Sadrita404/Nano-Spark/BILL/bill 1.png

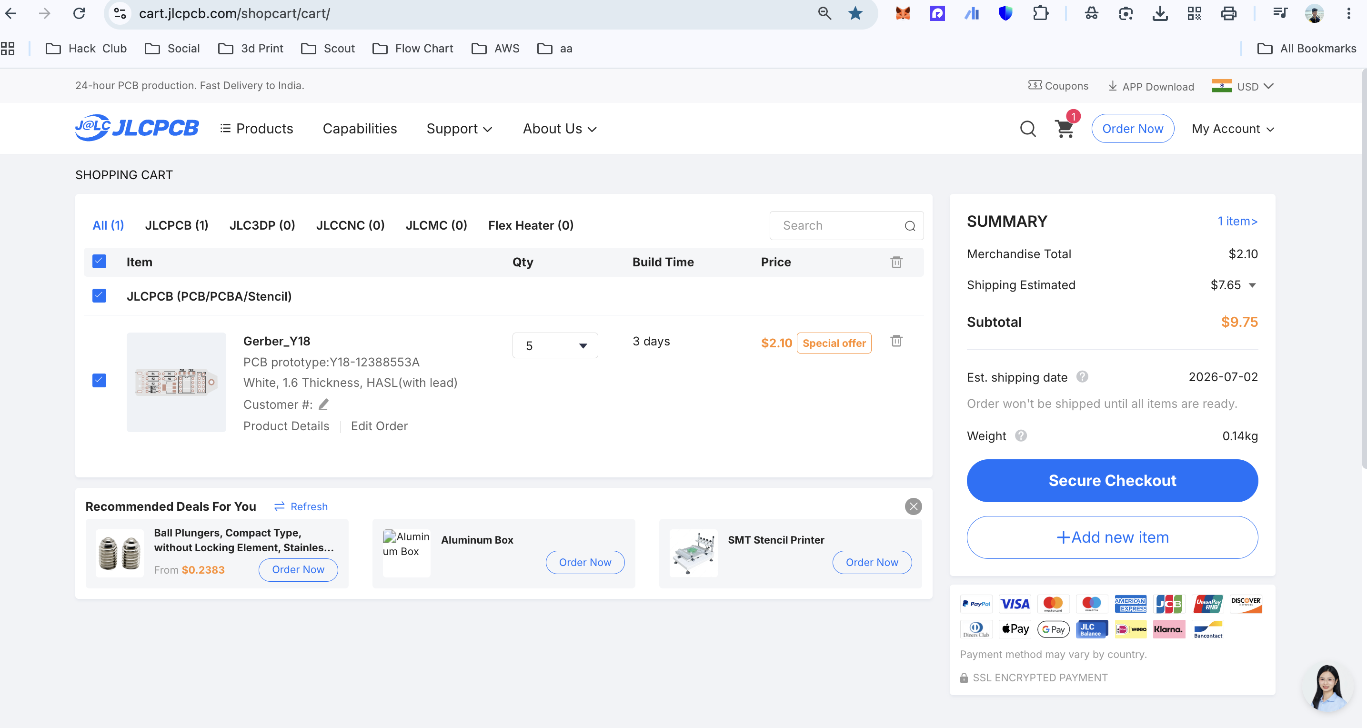
BILL/bill 1.png
