Sadrita404/Nano-Spark/BILL/bill 2.png

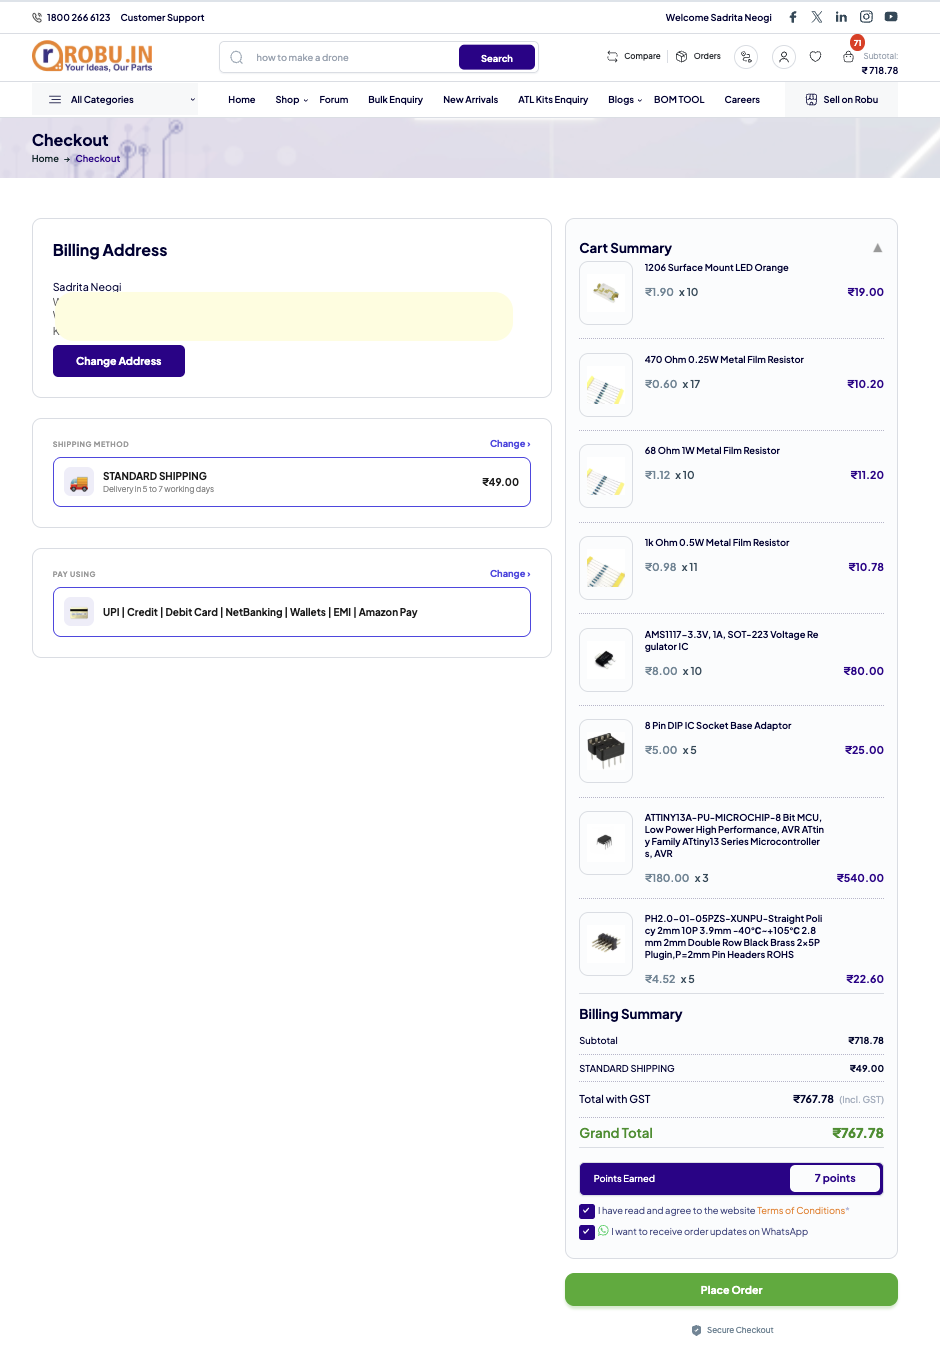
BILL/bill 2.png
