Sadrita404/Nano-Spark/BILL/bill 3.png

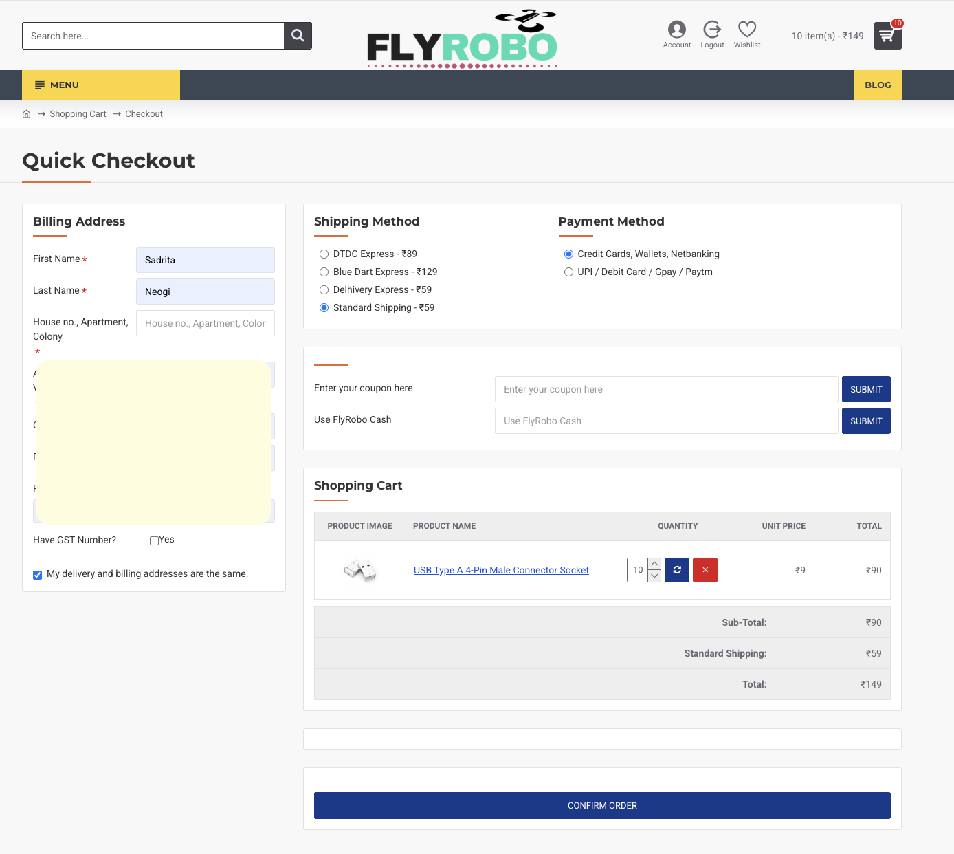
BILL/bill 3.png
