Sadrita404/Nano-Spark/Images/1.png

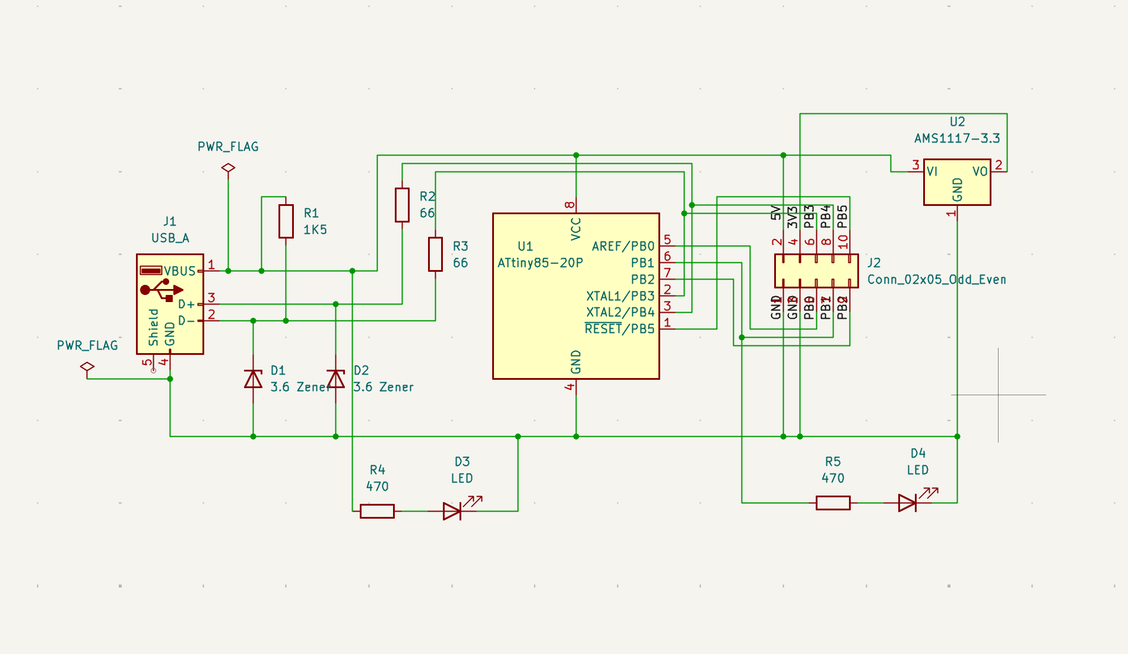
Images/1.png
