Sadrita404/Nano-Spark/Images/2.png

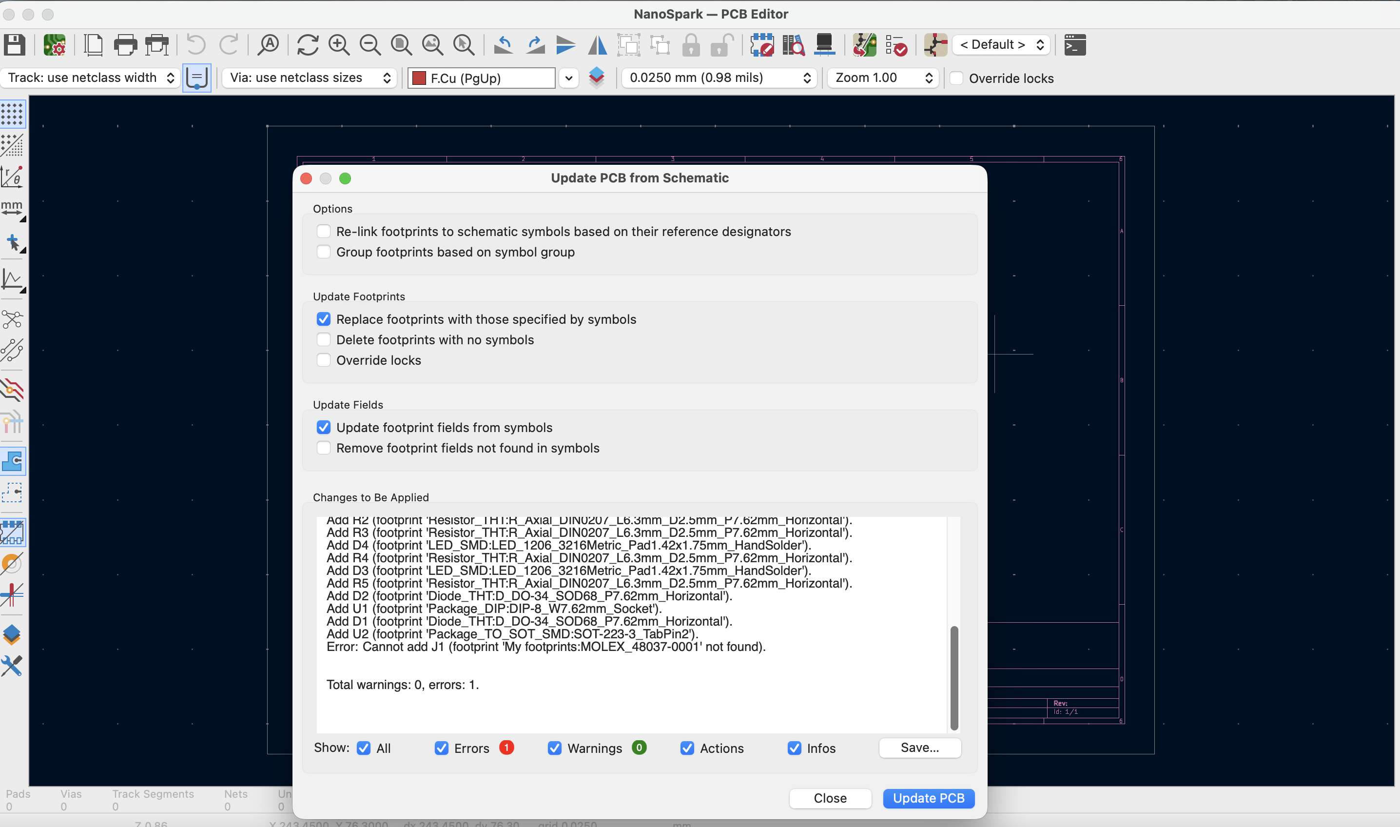
Images/2.png
