Sadrita404/Nano-Spark/Images/3.png

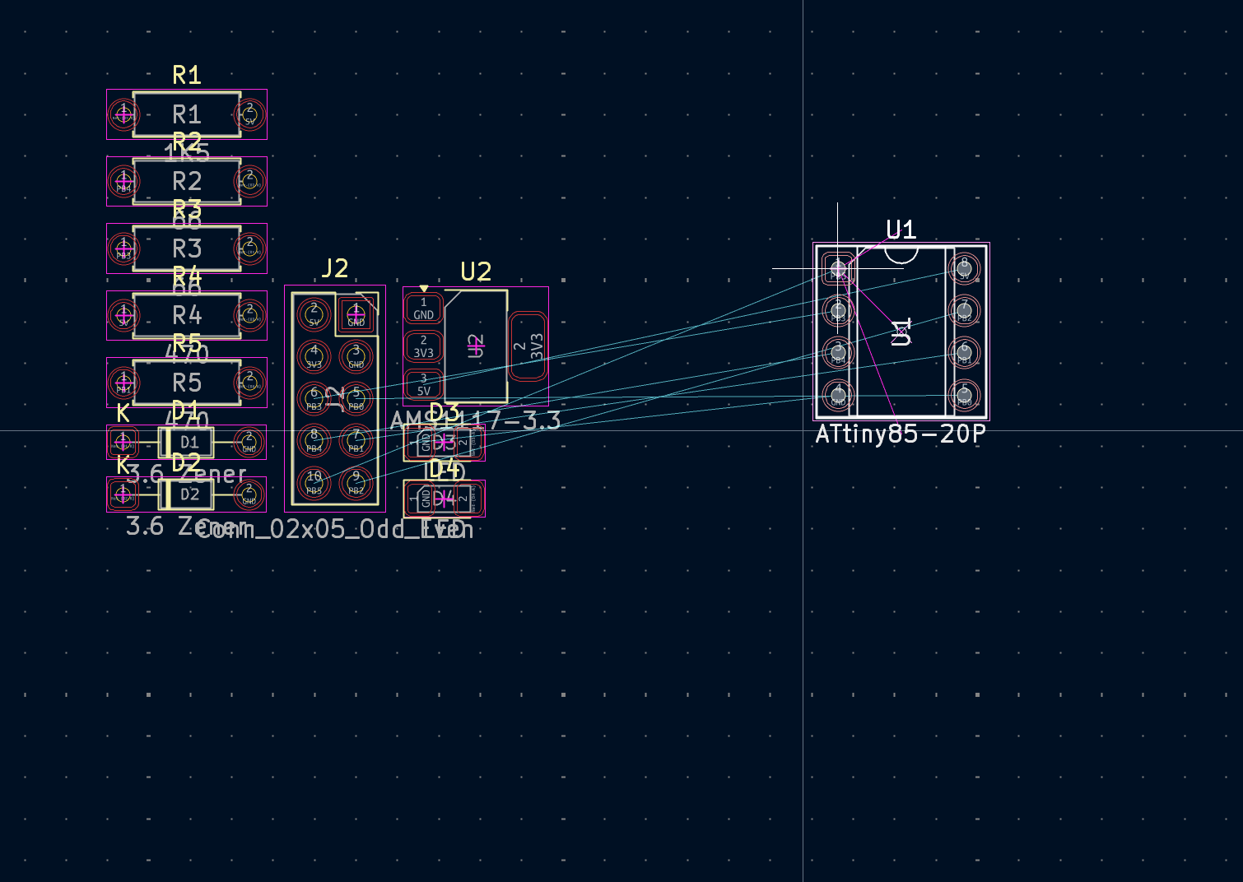
Images/3.png
