Sadrita404/Nano-Spark/Images/4.png

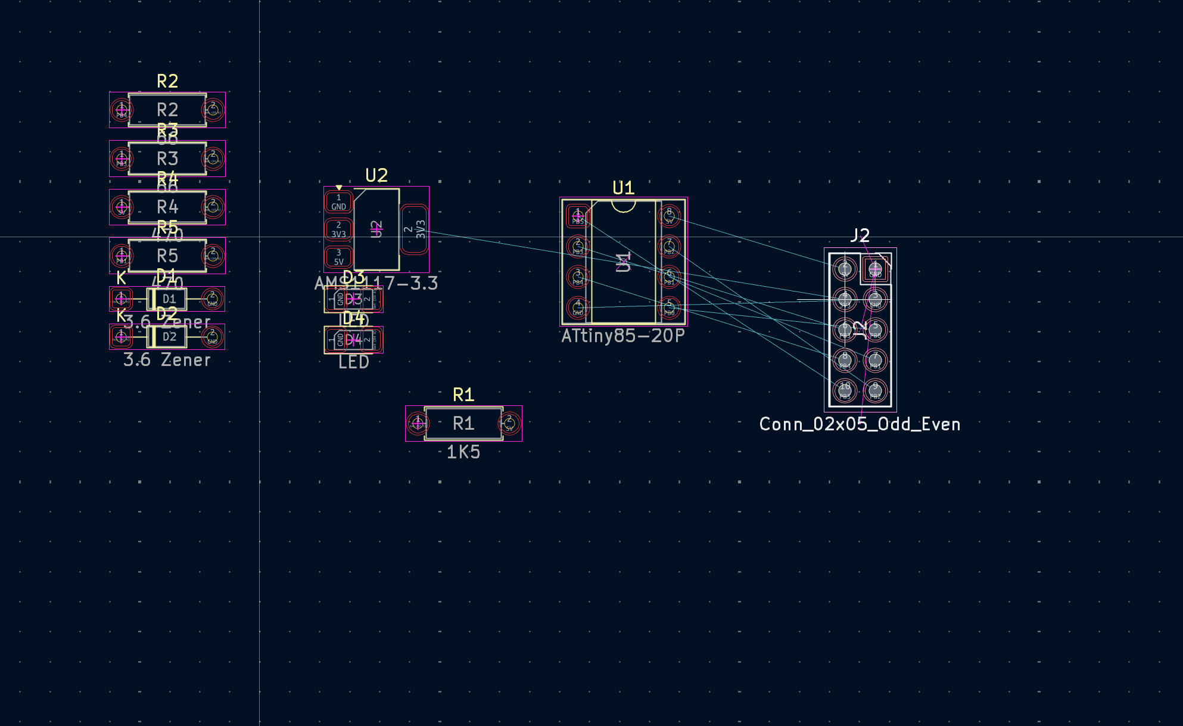
Images/4.png
