Sadrita404/Nano-Spark/Images/5.png

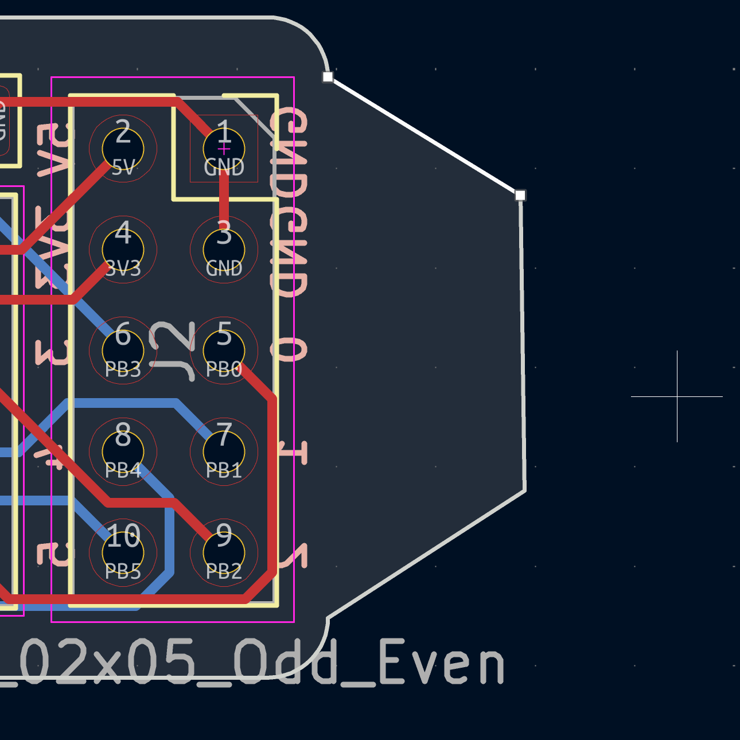
Images/5.png
