Sadrita404/Nano-Spark/Images/6.png

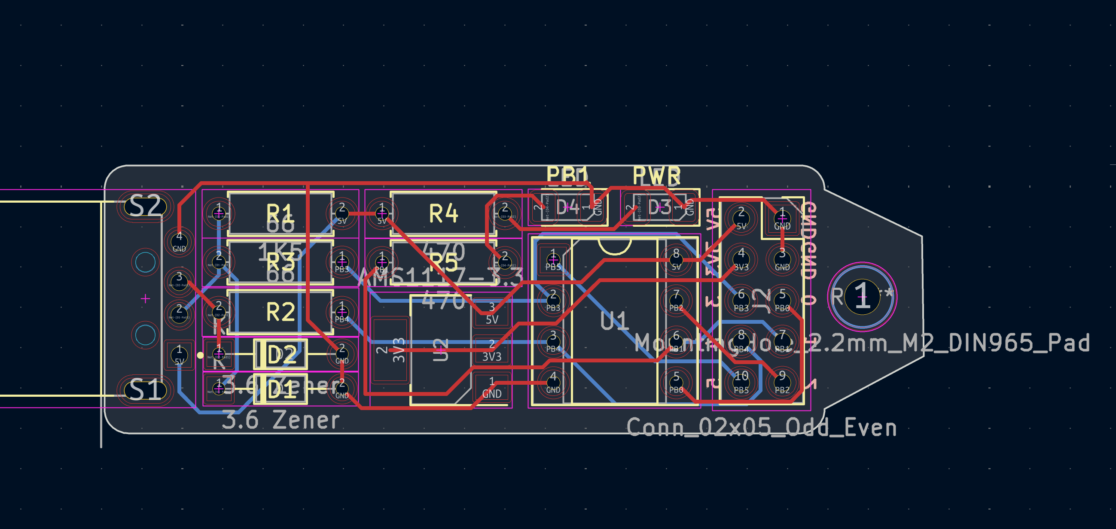
Images/6.png
