Sadrita404/Nano-Spark/Images/7.png

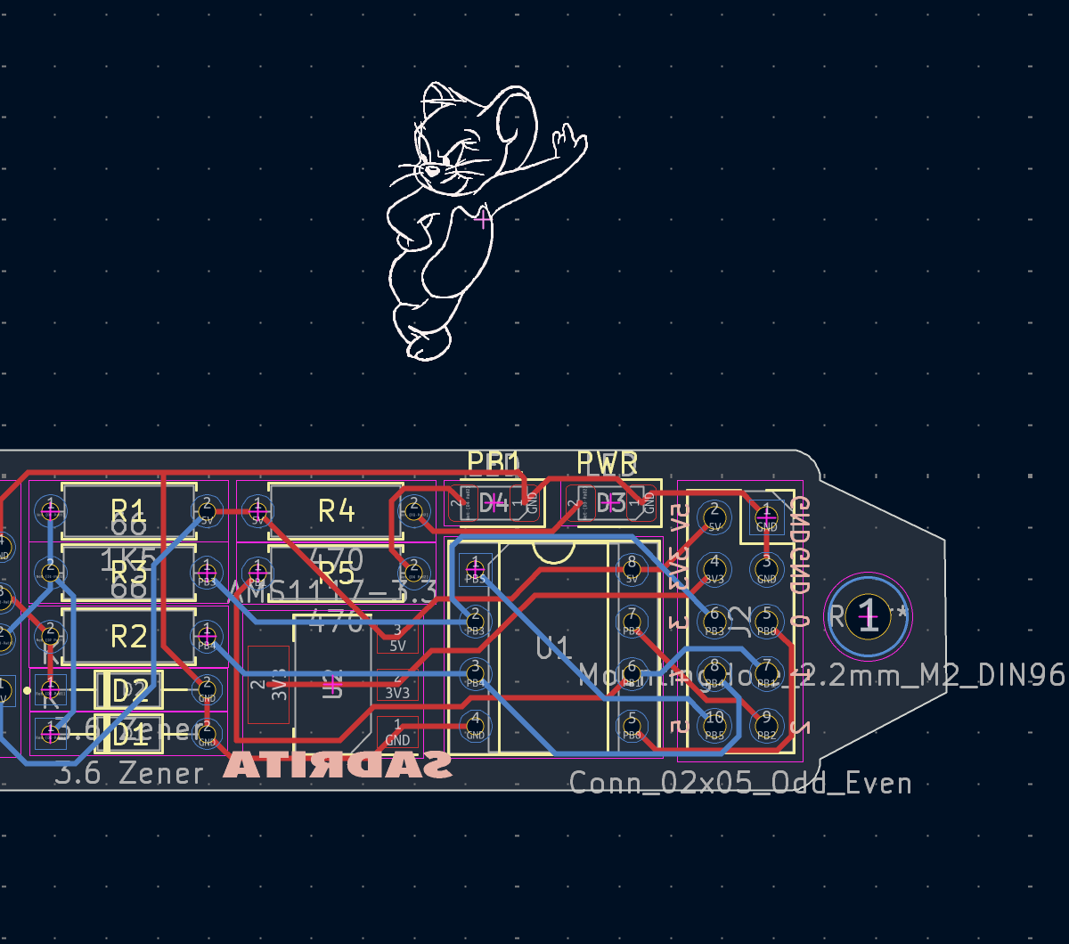
Images/7.png
