Sadrita404/Nano-Spark/Images/8.png

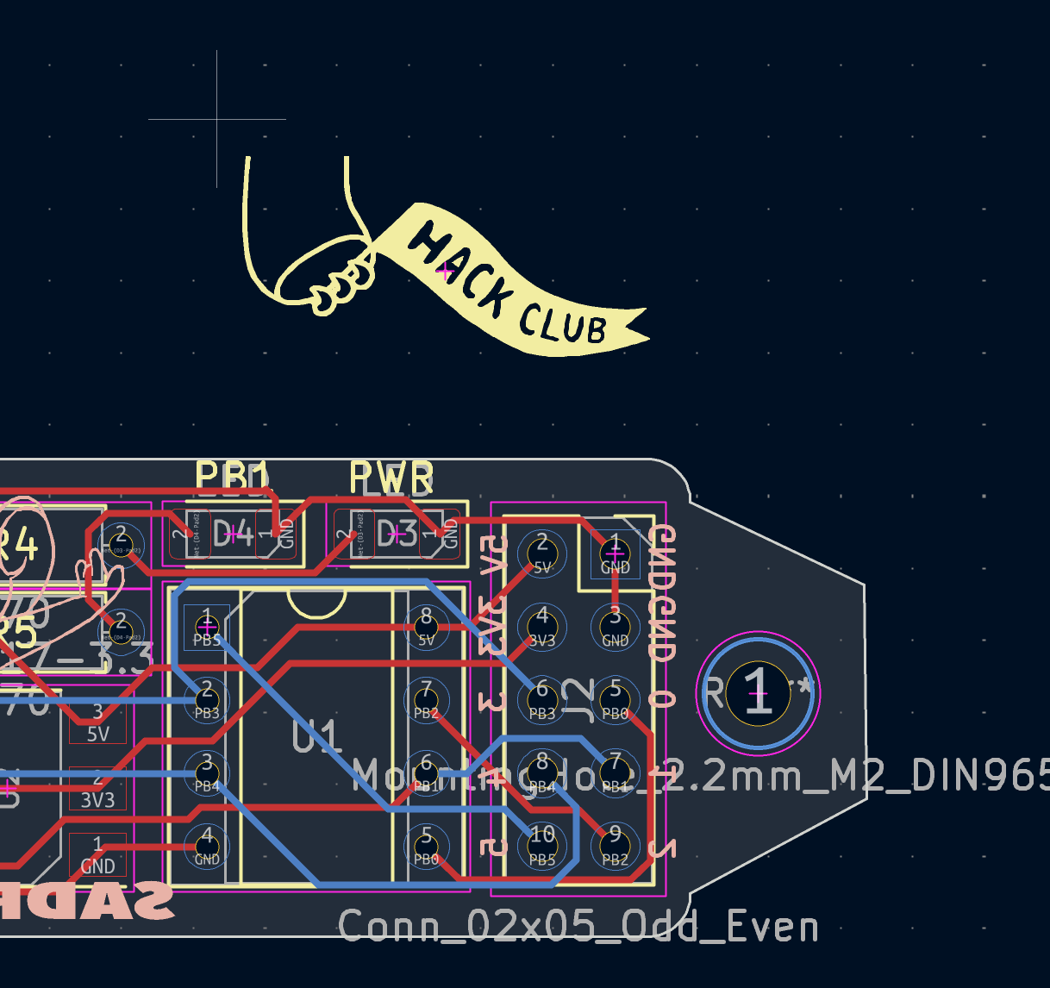
Images/8.png
