Sadrita404/Nano-Spark/Images/9.png

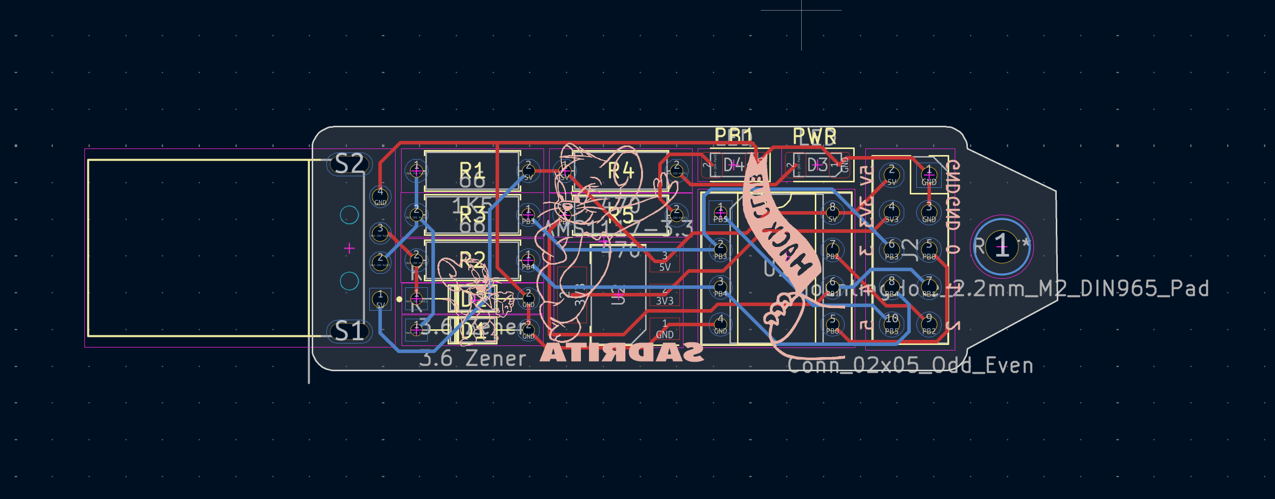
Images/9.png
