Sadrita404/Nano-Spark/Images/10.png

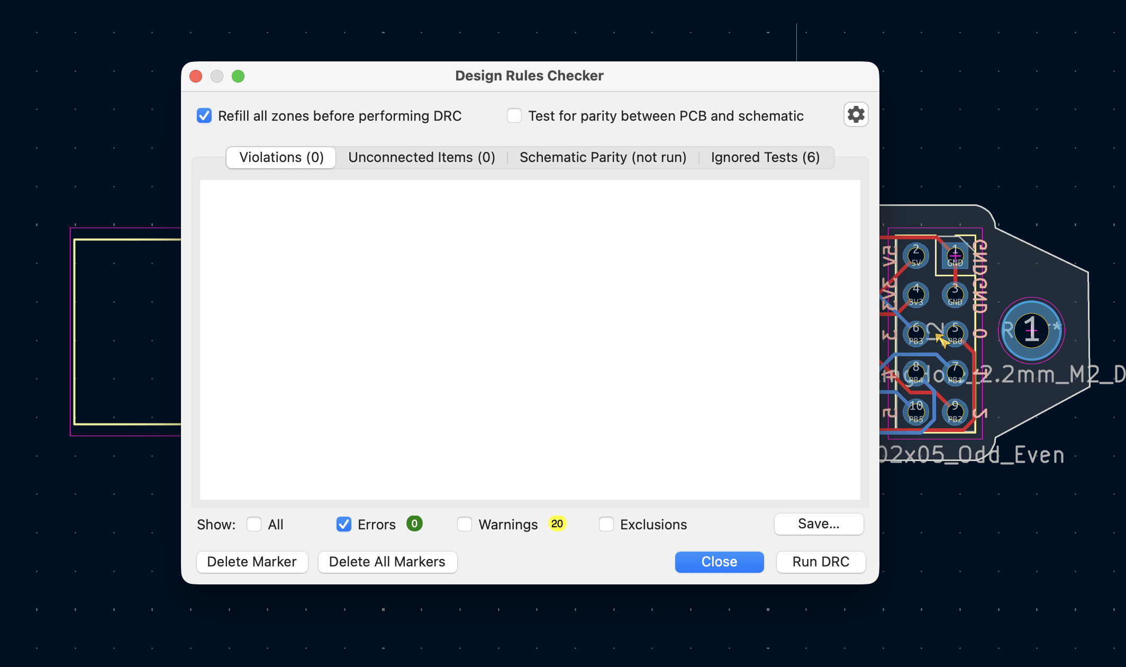
Images/10.png
