Sadrita404/Nano-Spark/Images/11.png

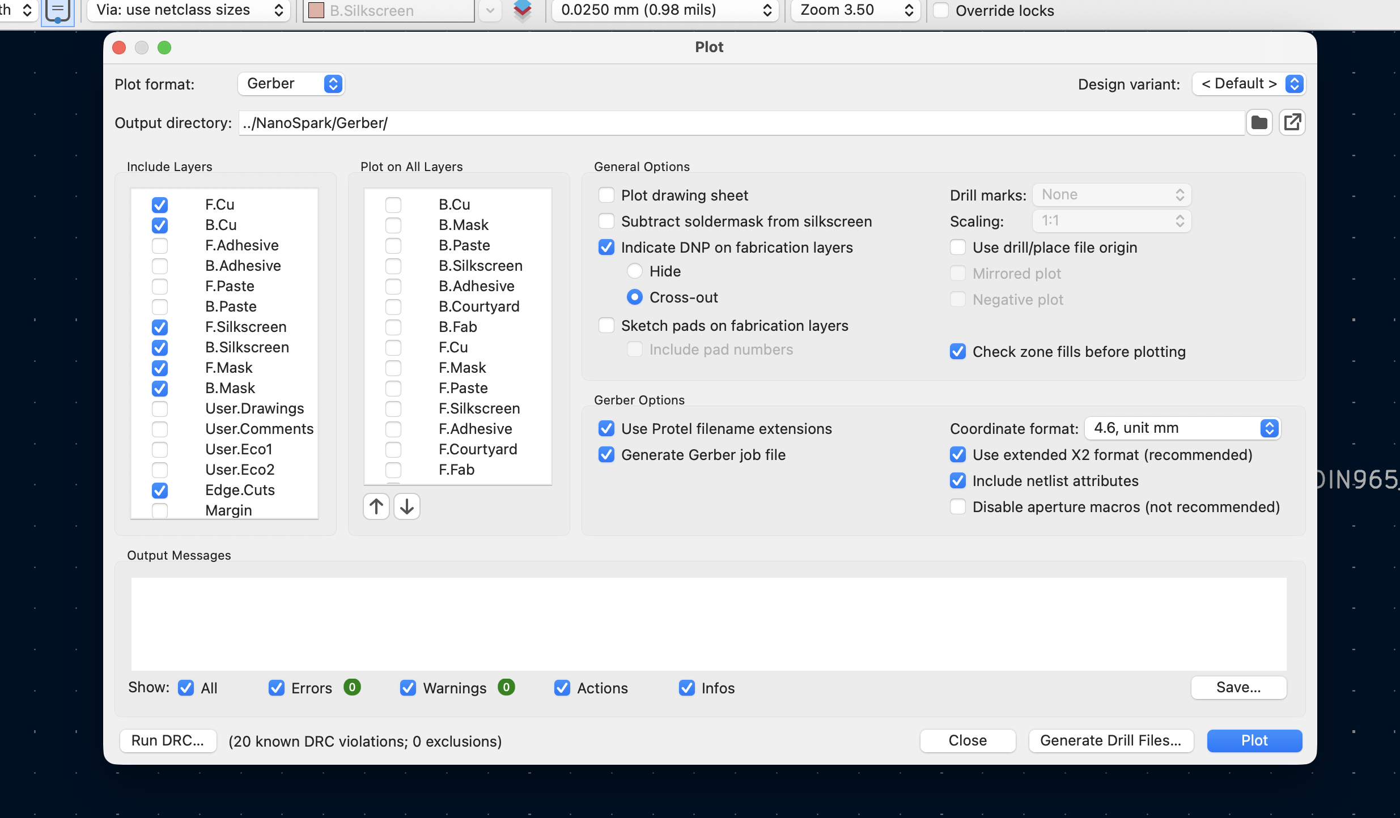
Images/11.png
